MarkD833/RCBUS-68xxx/boards/RC207-68000_BOOTROM_RAM/readme.md

# BOOT ROM & RAM board - 1M ROM + 1M RAM

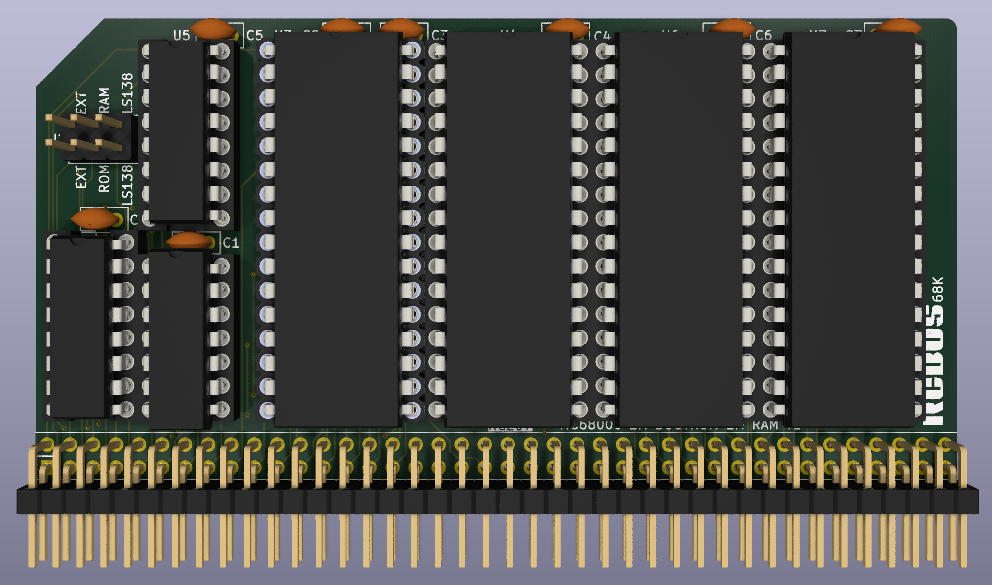
[picture p16: images/RC207-1.png]


The additional 2 chips hidden under one of the ROMs.

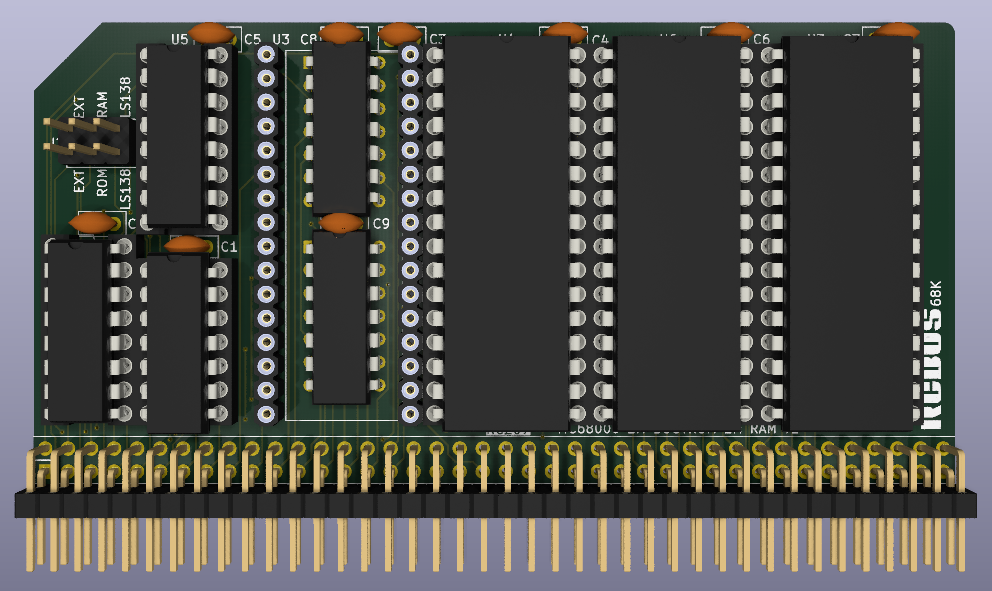
[picture p17: images/RC207-2.png]


# Details
This is a 3D render of my new BOOT ROM & RAM board. It is almost identical to my RC107 board with a couple of exceptions.

I'm experimenting with moving the BOOT ROM so that RAM can be located at address 0x000000. This board places the ROMs at address 0x000000 at reset. The ROMs stay mapped to this address until the first write is detected when the ROMs get mapped to addresses 0x700000..0x7FFFFF and the RAMs become available at addresses 0x000000..0x0FFFFF until the next reset. 

This memory board requires a software write to remap the memory chips.

This is very much a prototype at the moment and I need to see if the manual write works or causes issues.

**NOTE:** Work on this board has been abandoned after the success of RC208 which switches ROM & RAM automatically.
