MarkD833/RCBUS-68xxx/asm_code/ehBASIC_3.54/README.md

# EhBASIC68k for RCBus 68000

Enhanced 68k BASIC Version 3.54 for my RCBus 68000 system.

Assemble using EASy68K.

Original text follows:

---

 EhBASIC68

 Enhanced BASIC is a BASIC interpreter for the 68k family microprocessors. It  
 is constructed to be quick and powerful and easily ported between 68k systems.  
 It requires few resources to run and includes instructions to facilitate easy  
 low level handling of hardware devices. It also retains most of the powerful  
 high level instructions from similar BASICs.  

 EhBASIC is copyright Lee Davison 2002 - 2012 and free for educational or  
 personal use only.  
 For commercial use please contact me at leeedavison@lgooglemail.com for conditions.  

 For more information on EhBASIC68, other versions of EhBASIC and other projects  
 please visit my site at ..  

	 http://mycorner.no-ip.org/index.html  

https://github.com/jefftranter/68000/tree/master/ehbasic

---
## Retro Computing » MOS Technology 6502 » Lee Davison’s website
http://retro.hansotten.nl/6502-sbc/lee-davison-web-site/
