MarkD833/RCBUS-68xxx/asm_code/SC611/25LC256_1.png

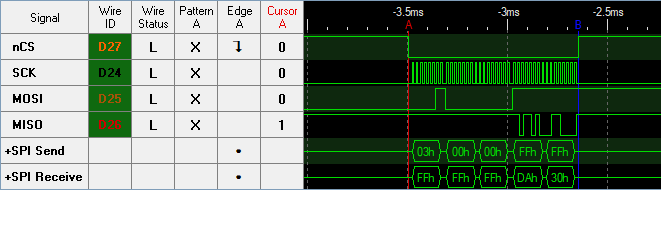
asm_code/SC611/25LC256_1.png
