MarkD833/RCBUS-68xxx/asm_code/SC611/25LC256_2.png

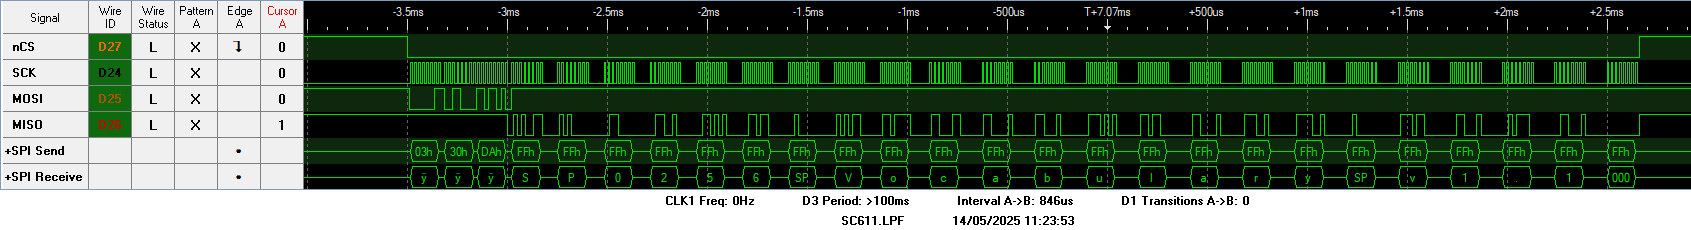
asm_code/SC611/25LC256_2.png
