MarkD833/RCBUS-68xxx/images/Board_Set_2.JPG

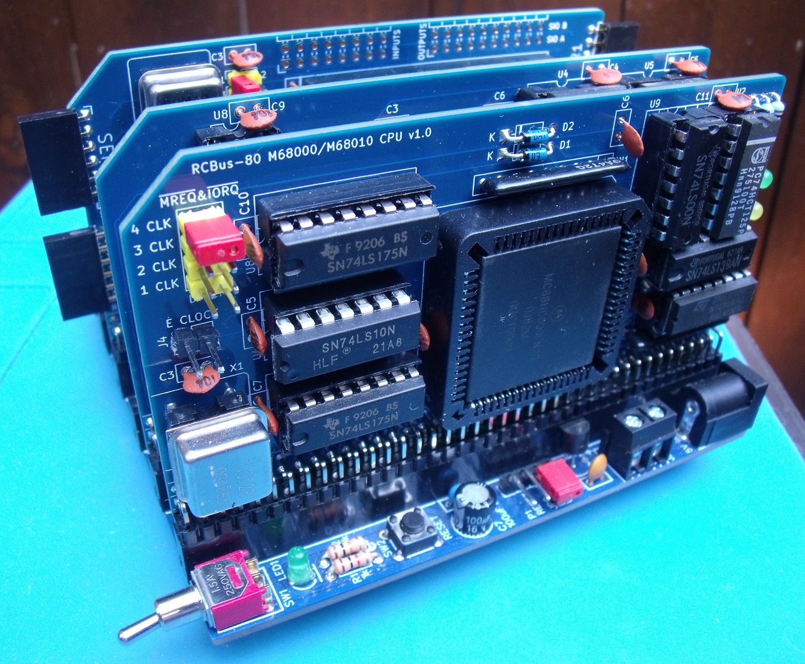
images/Board_Set_2.JPG
