MarkD833/RCBUS-68xxx/images/MC68302_Pins_1.JPG

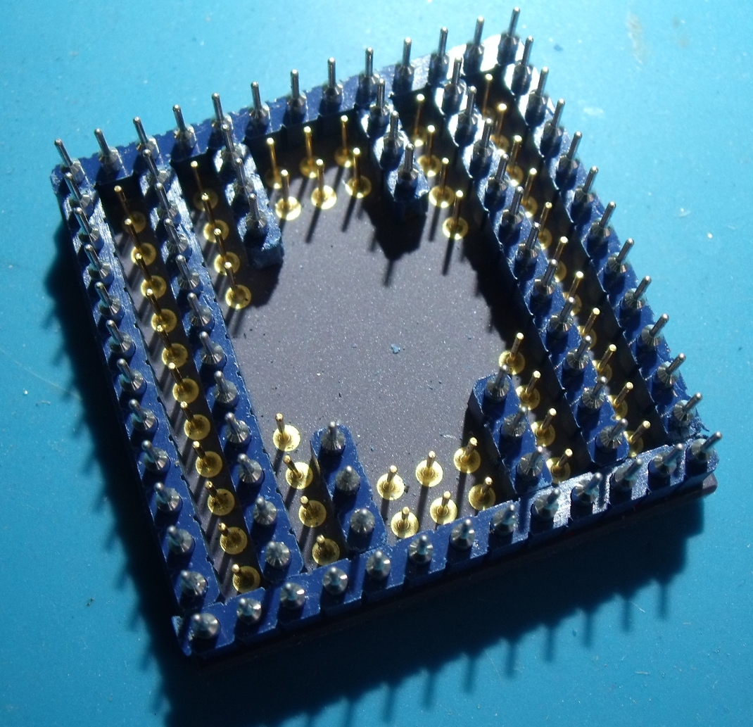
images/MC68302_Pins_1.JPG
