MarkD833/RCBUS-68xxx/images/PIO_Rear.JPG

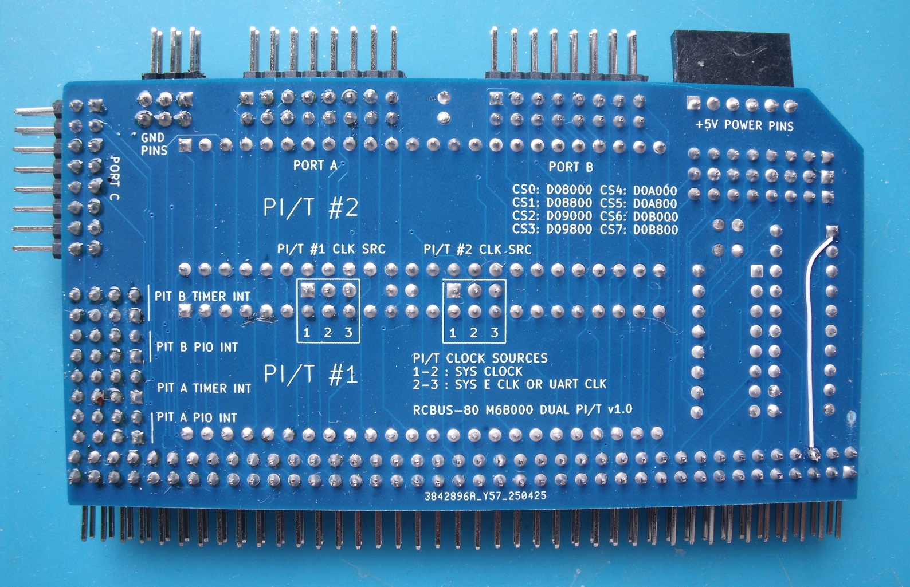
images/PIO_Rear.JPG
