MarkD833/RCBUS-68xxx/images/Processor_Rear.JPG

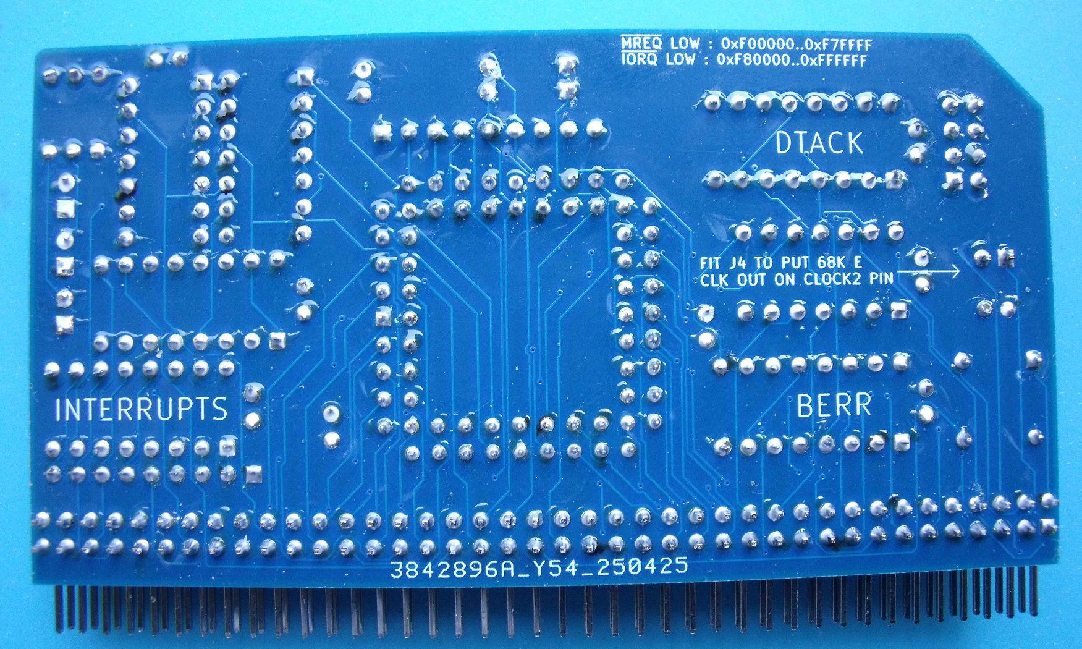
images/Processor_Rear.JPG
