MarkD833/RCBUS-68xxx/images/RC200-Dev_Backplane.png

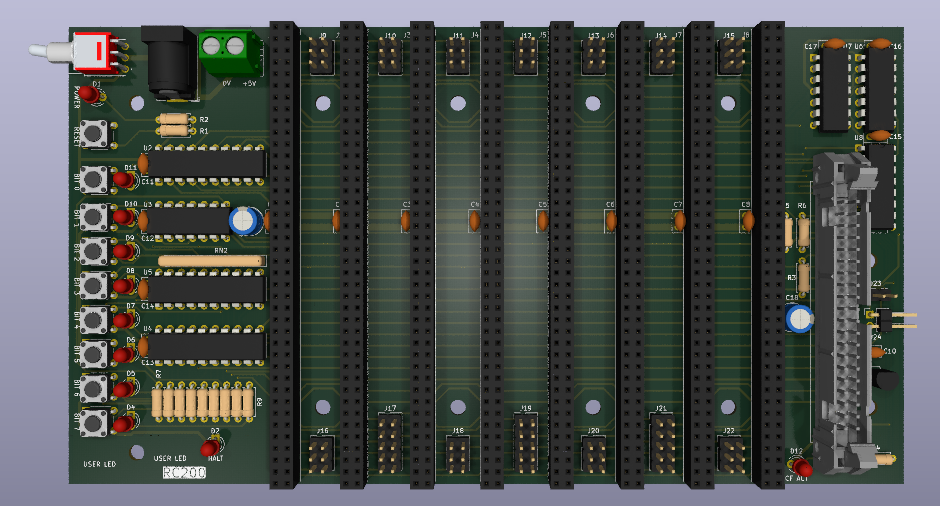
images/RC200-Dev_Backplane.png
