MarkD833/RCBUS-68xxx/images/RC201-68000_CPU_VI_Board_v2.png

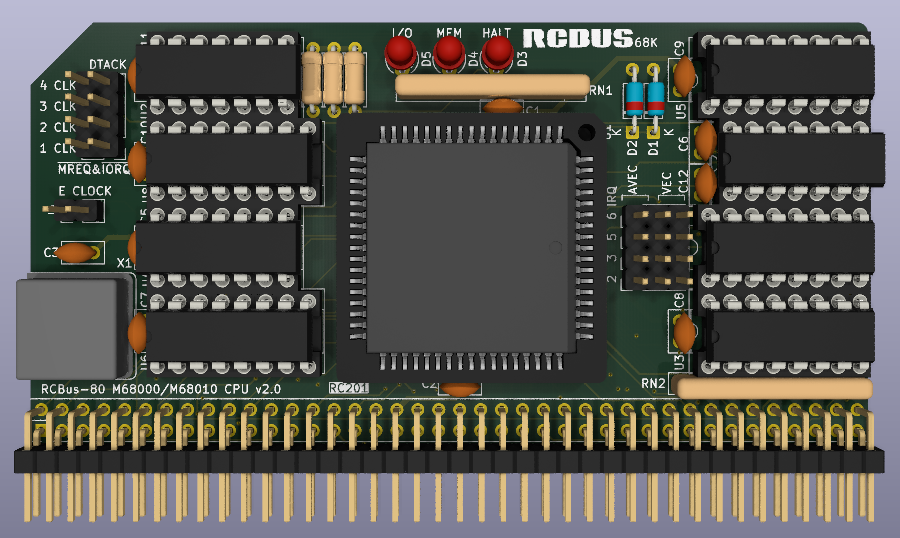
images/RC201-68000_CPU_VI_Board_v2.png
