MarkD833/RCBUS-68xxx/images/RC205-68020_CPU_1.png

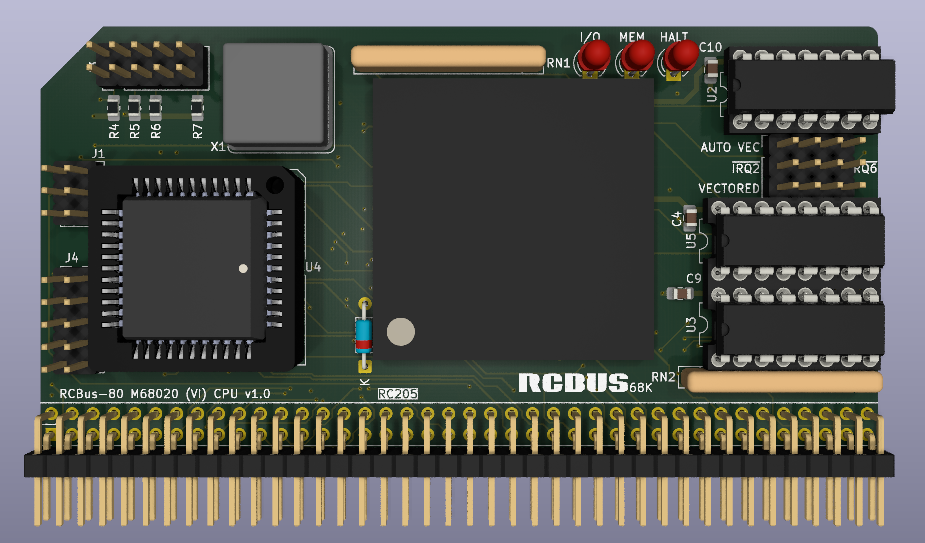
images/RC205-68020_CPU_1.png
