MarkD833/RCBUS-68xxx/images/ROM_RAM_Rear.JPG

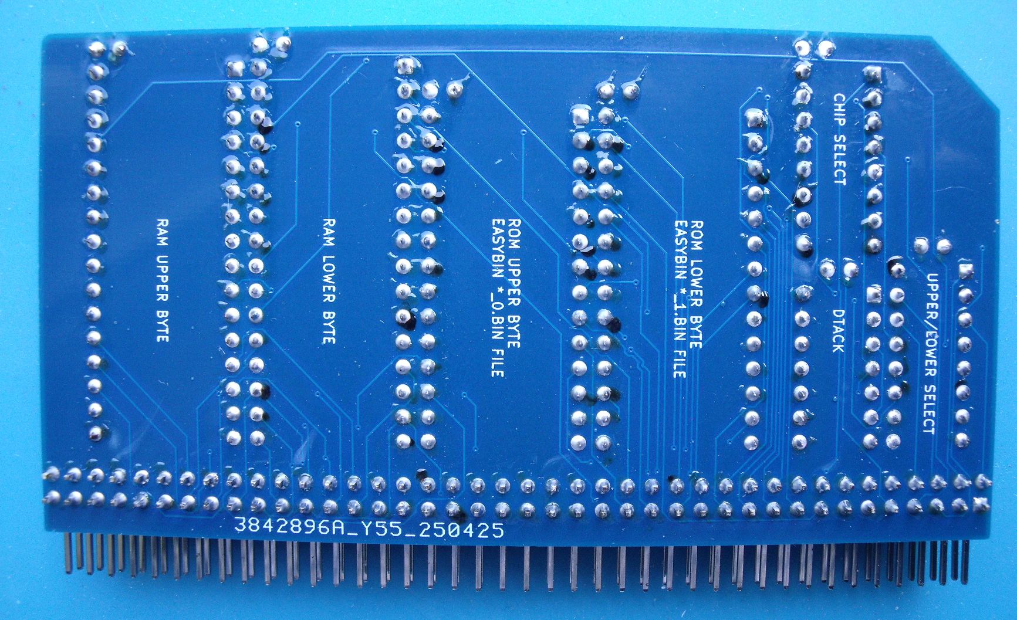
images/ROM_RAM_Rear.JPG
