MarkD833/RCBUS-68xxx/images/S2_68000_PIO_VI_Board.png

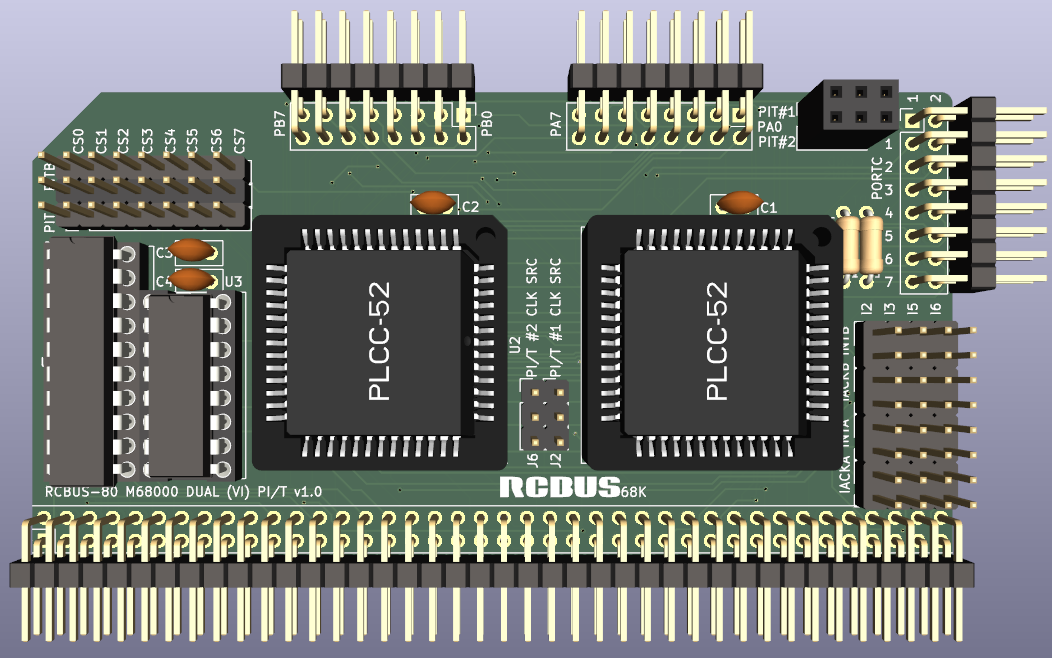
images/S2_68000_PIO_VI_Board.png
