MarkD833/RCBUS-68xxx/images/Serial_Rear.JPG

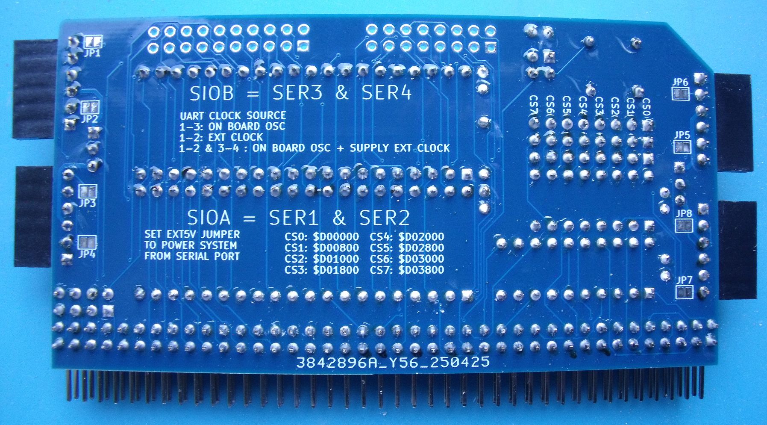
images/Serial_Rear.JPG
