MarkD833/RCBUS-68xxx/boards/RC200-Dev_Backplane/RC200-Dev_Backplane.pdf

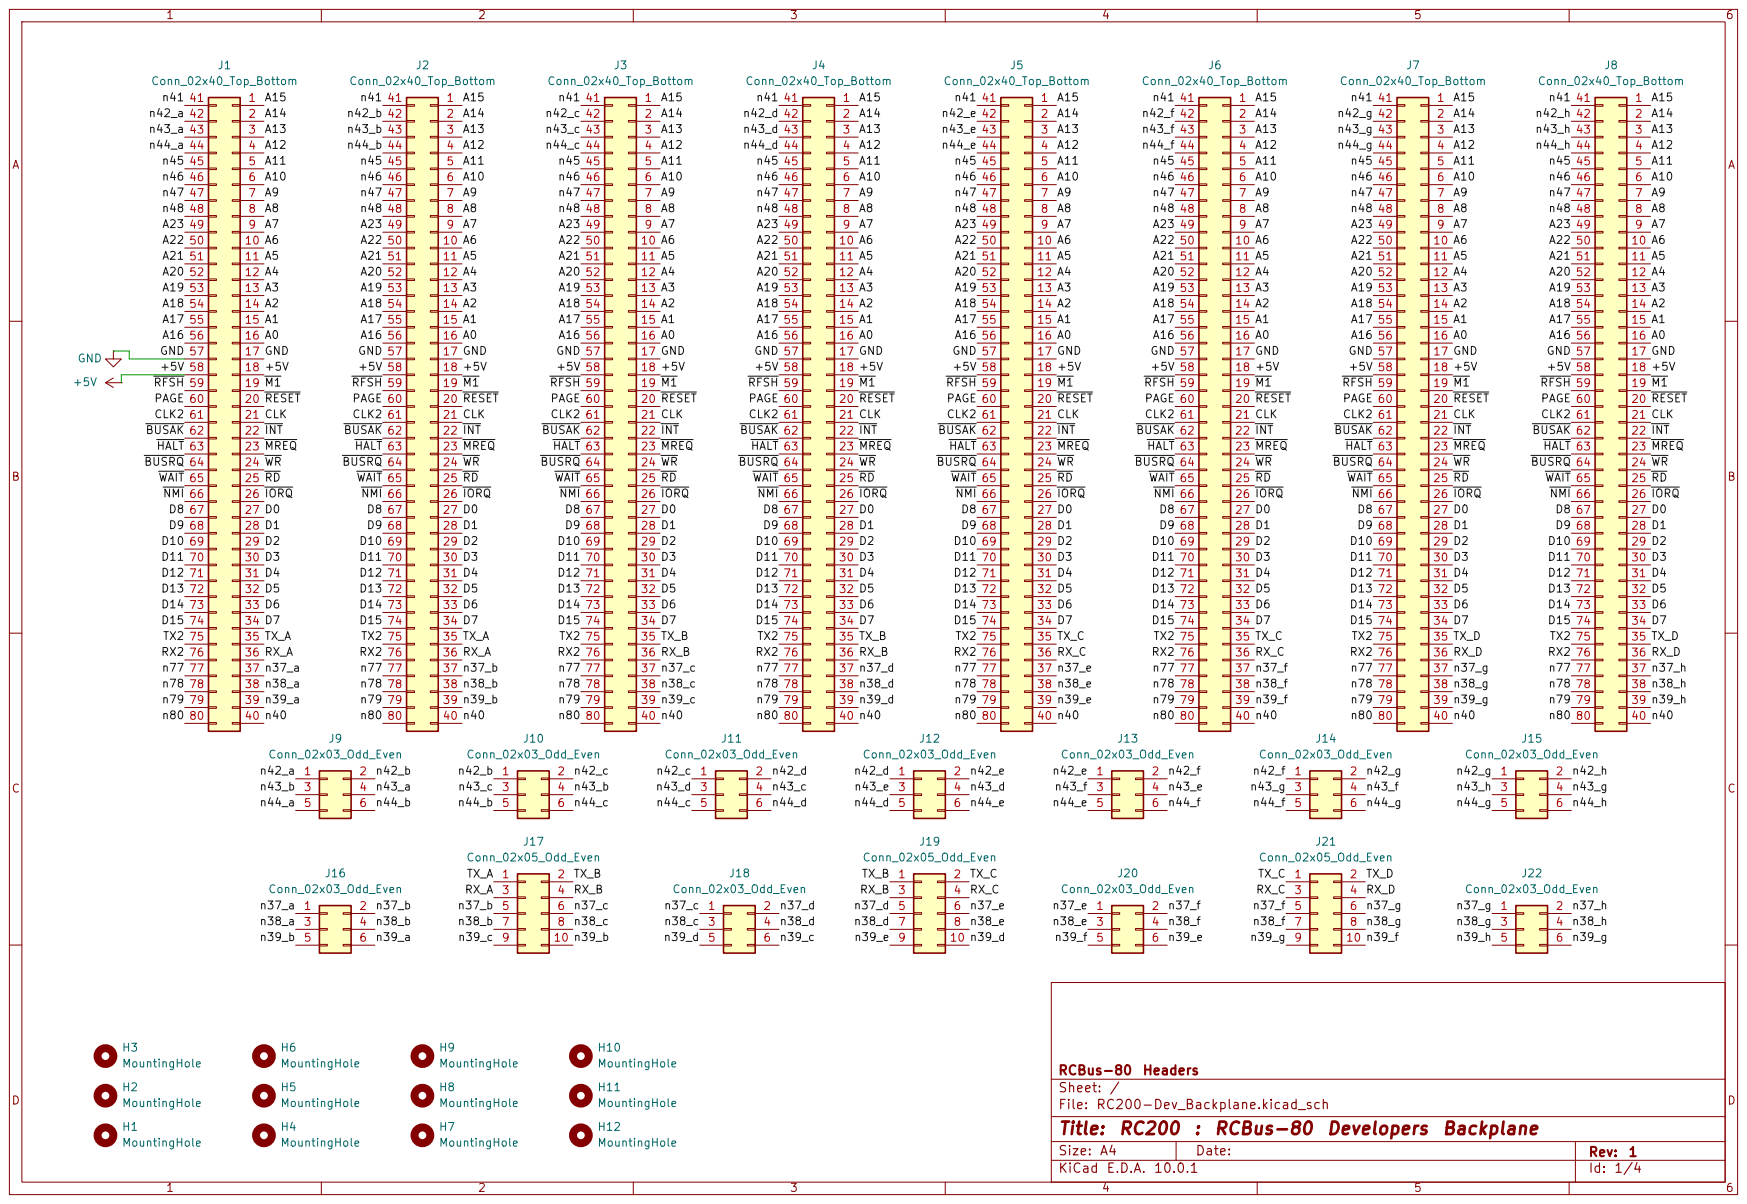
[picture p51: page 1]

RCBus-80 Headers
Sheet: /
File: RC200-Dev_Backplane.kicad_sch
Title: RC200 : RCBus-80 Developers Backplane

Size: A4 | Rev: 1
KiCad E.D.A. 10.0.1 | Id: 1/4

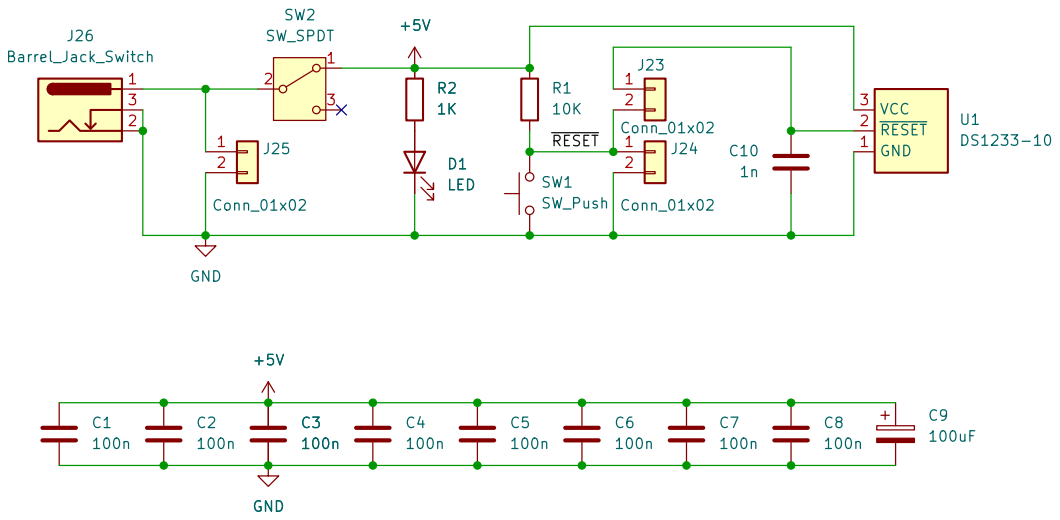
[picture p52: page 2]

Power
Sheet: /
File: power.kicad_sch
Title: RC200 : RCBus-80 Developers Backplane

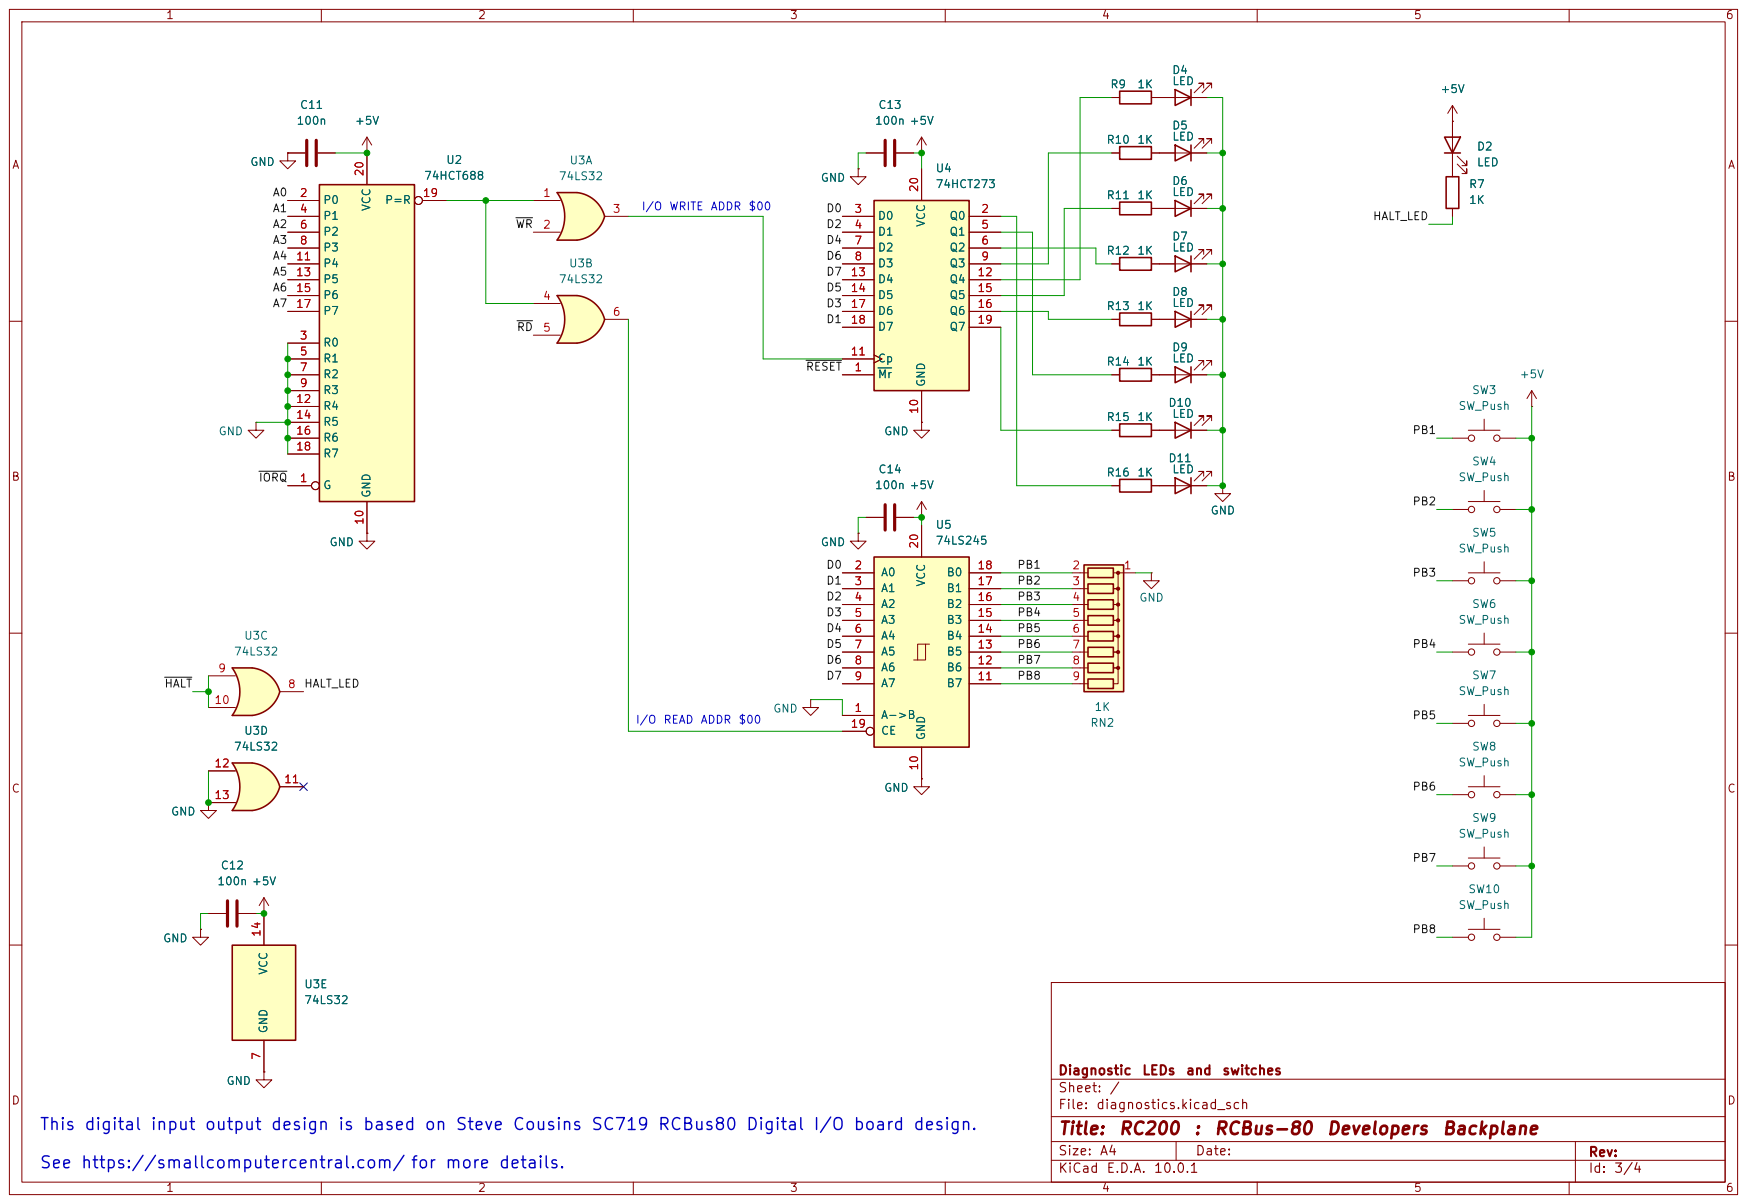
[picture p53: page 3]

Diagnostic LEDs and switches
Sheet: /
File: diagnostics.kicad_sch
Title: RC200 : RCBus-80 Developers Backplane

This digital input output design is based on Steve Cousins SC719 RCBus80 Digital I/O board design.

See https://smallcomputercentral.com/ for more details.

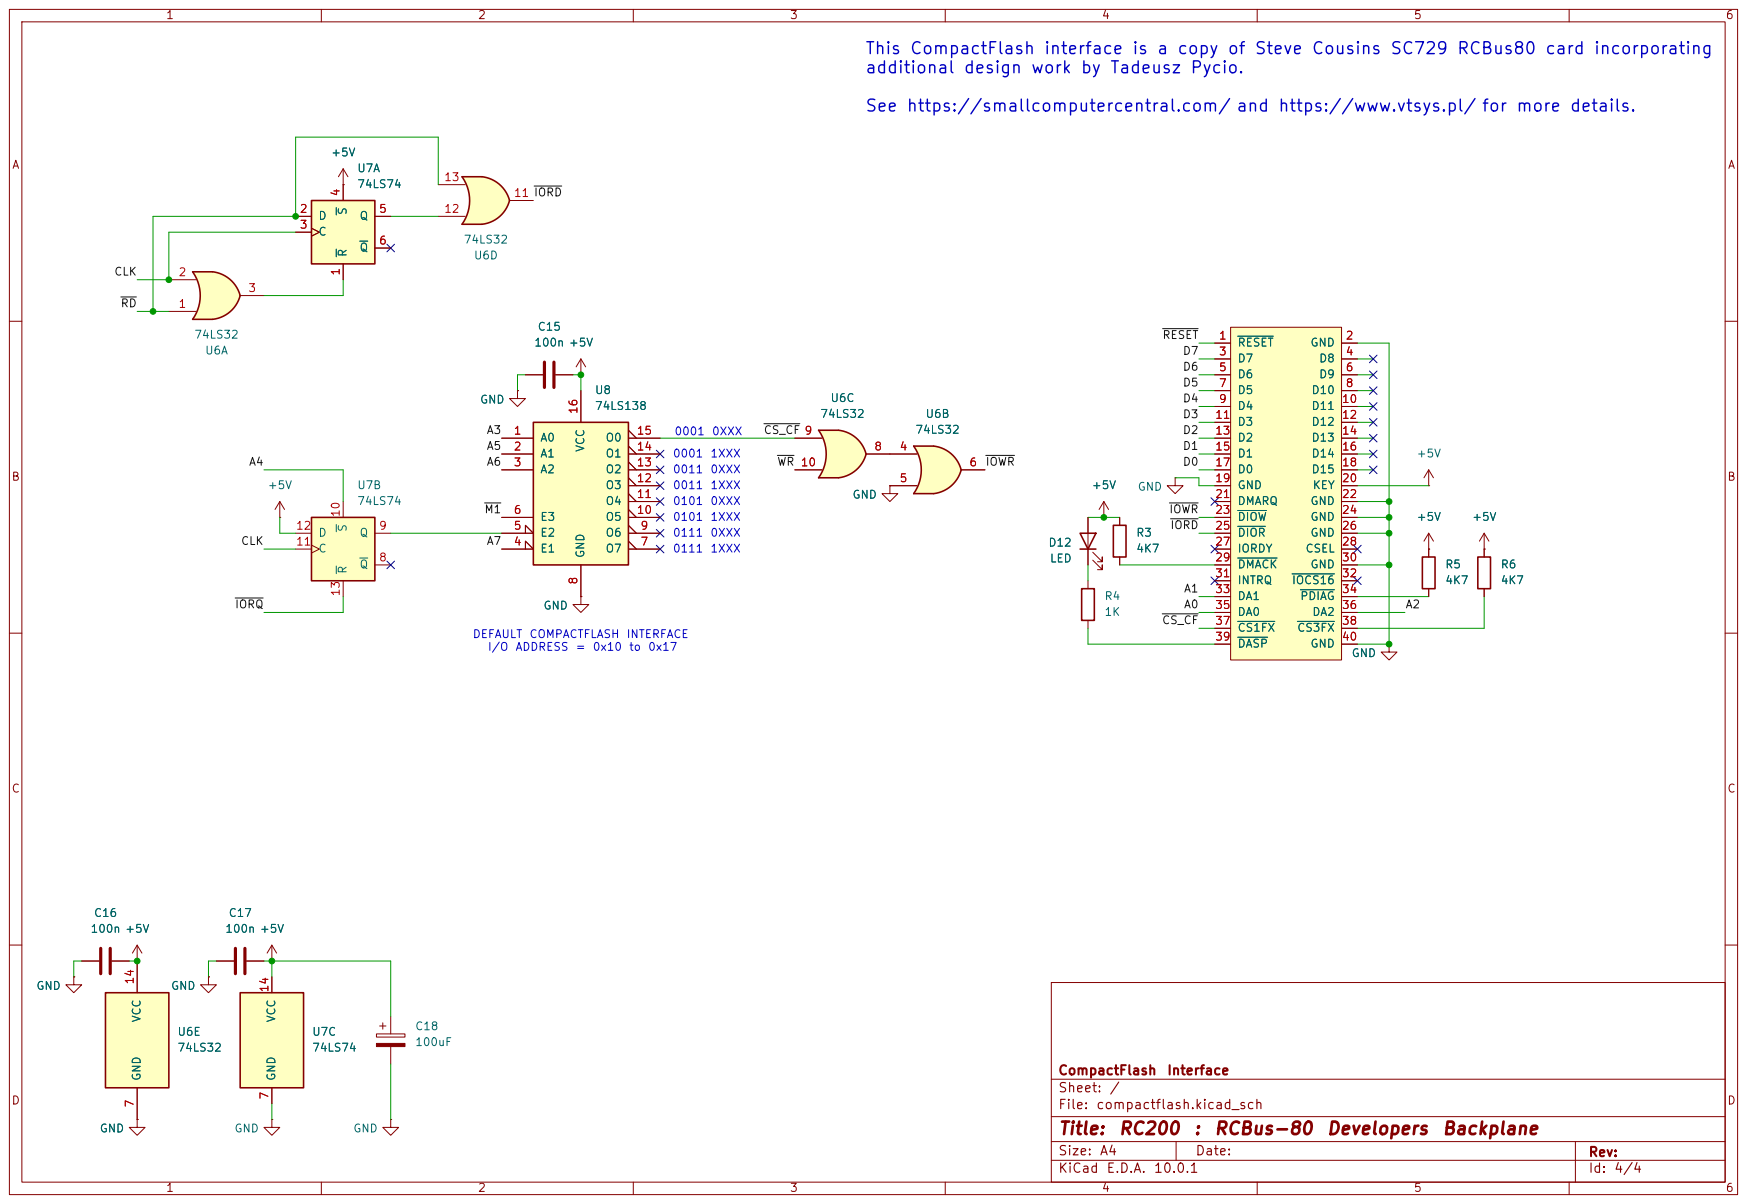
[picture p54: page 4]

additional design work by Tadeusz Pycio.

See https://smallcomputercentral.com/ and https://www.vtsys.pl/ for more details. D12

CompactFlash Interface
Sheet: /
File: compactflash.kicad_sch
Title: RC200 : RCBus-80 Developers Backplane
