MarkD833/RCBUS-68xxx/boards/RC208-68000_BOOTROM_RAM/RC208-68000_BOOTROM_RAM_2.pdf

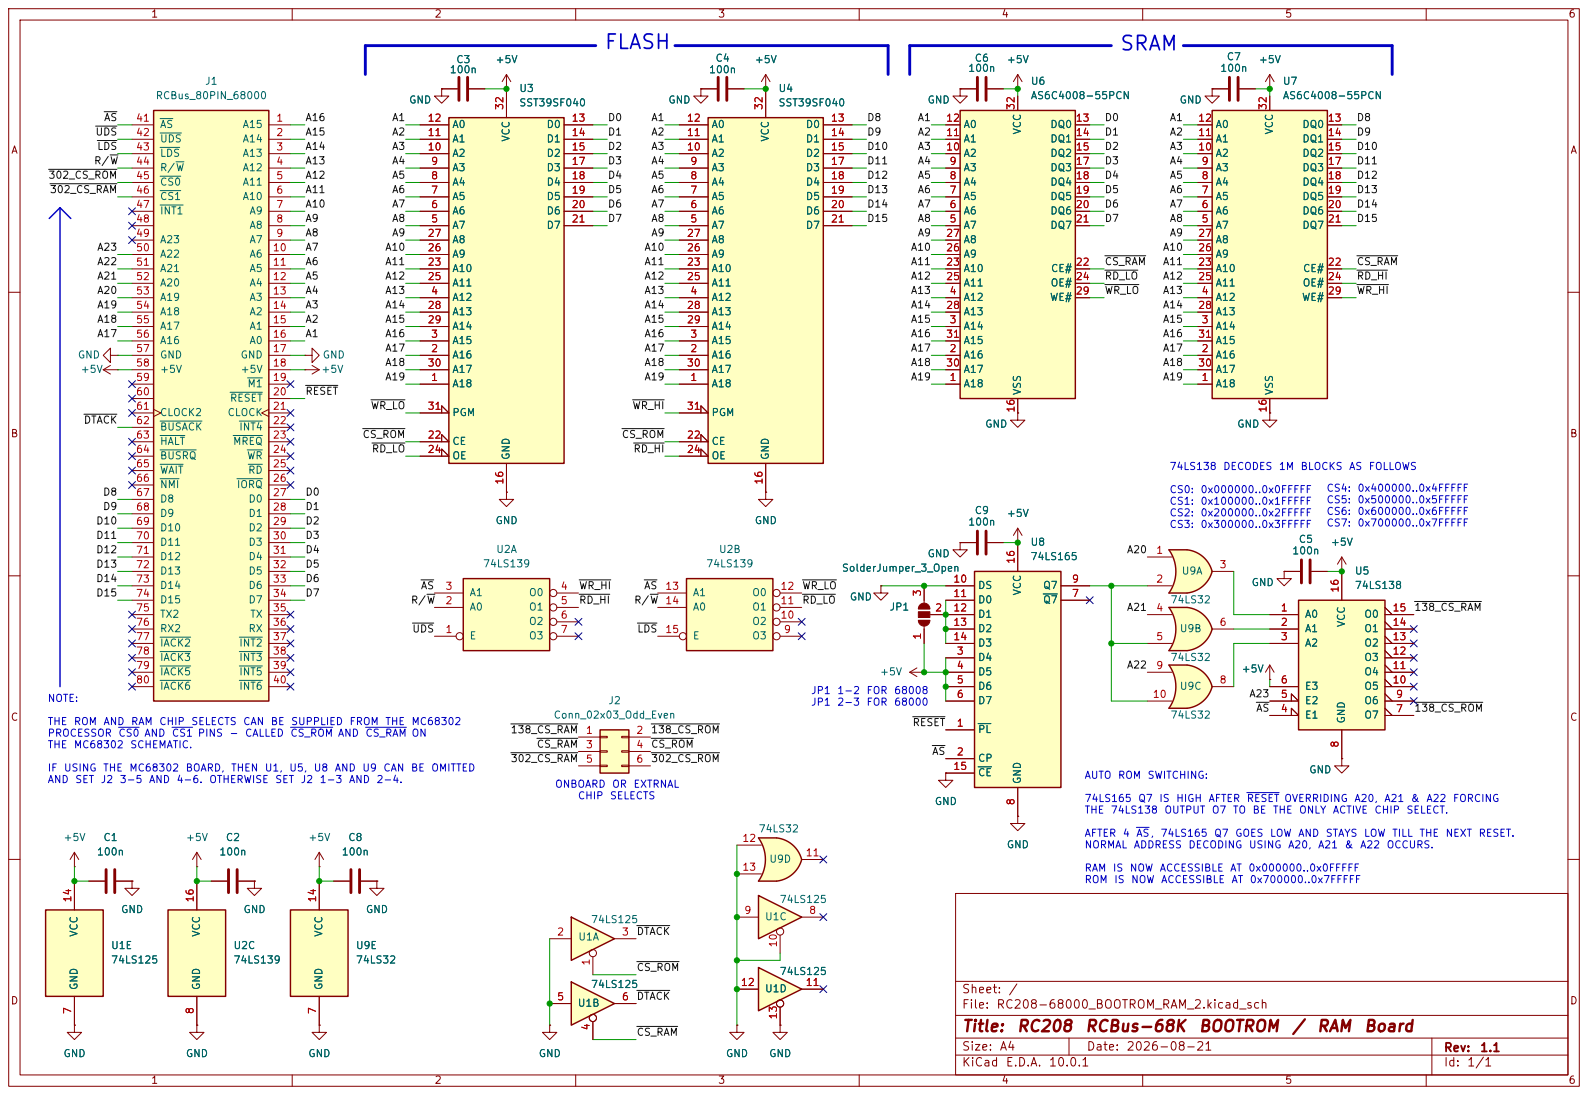
[picture p55: page 1]

74LS138 DECODES 1M BLOCKS AS FOLLOWS CS0: 0x000000..0x0FFFFF CS1: 0x100000..0x1FFFFF CS2: 0x200000..0x2FFFFF CS3: 0x300000..0x3FFFFF FLASH
AS6C4008-55PCN VSS 16 VCC 32
74LS138 VSS 16 VCC 32

CS4: 0x400000..0x4FFFFF CS5: 0x500000..0x5FFFFF CS6: 0x600000..0x6FFFFF CS7: 0x700000..0x7FFFFF NOTE: THE ROM AND RAM CHIP SELECTS CAN BE SUPPLIED FROM THE MC68302 PROCESSOR CS0 AND CS1 PINS - CALLED CS_ROM AND CS_RAM ON

THE 74LS138 OUTPUT O7 TO BE THE ONLY ACTIVE CHIP SELECT. AFTER 4 AS , 74LS165 Q7 GOES LOW AND STAYS LOW TILL THE NEXT RESET. NORMAL ADDRESS DECODING USING A20, A21 & A22 OCCURS. RAM IS NOW ACCESSIBLE AT 0x000000..0x0FFFFF ROM IS NOW ACCESSIBLE AT 0x700000..0x7FFFFF +5V U8

IF USING THE MC68302 BOARD, THEN U1, U5, U8 AND U9 CAN BE OMITTED
100n +5V GNDGND

ONBOARD OR EXTRNAL CHIP SELECTS

Sheet: /
File: RC208-68000_BOOTROM_RAM_2.kicad_sch
Title: RC208 RCBus-68K BOOTROM / RAM Board

Size: A4 | Rev: 1.1
KiCad E.D.A. 10.0.1 | Id: 1/1
