MarkD833/RCBUS-68xxx/boards/RC103_SIO_Board/68000_SIO_BOARD.kicad_pcb

## KiCad design boards/RC103_SIO_Board/68000_SIO_BOARD.kicad_pcb (2025-05-10)

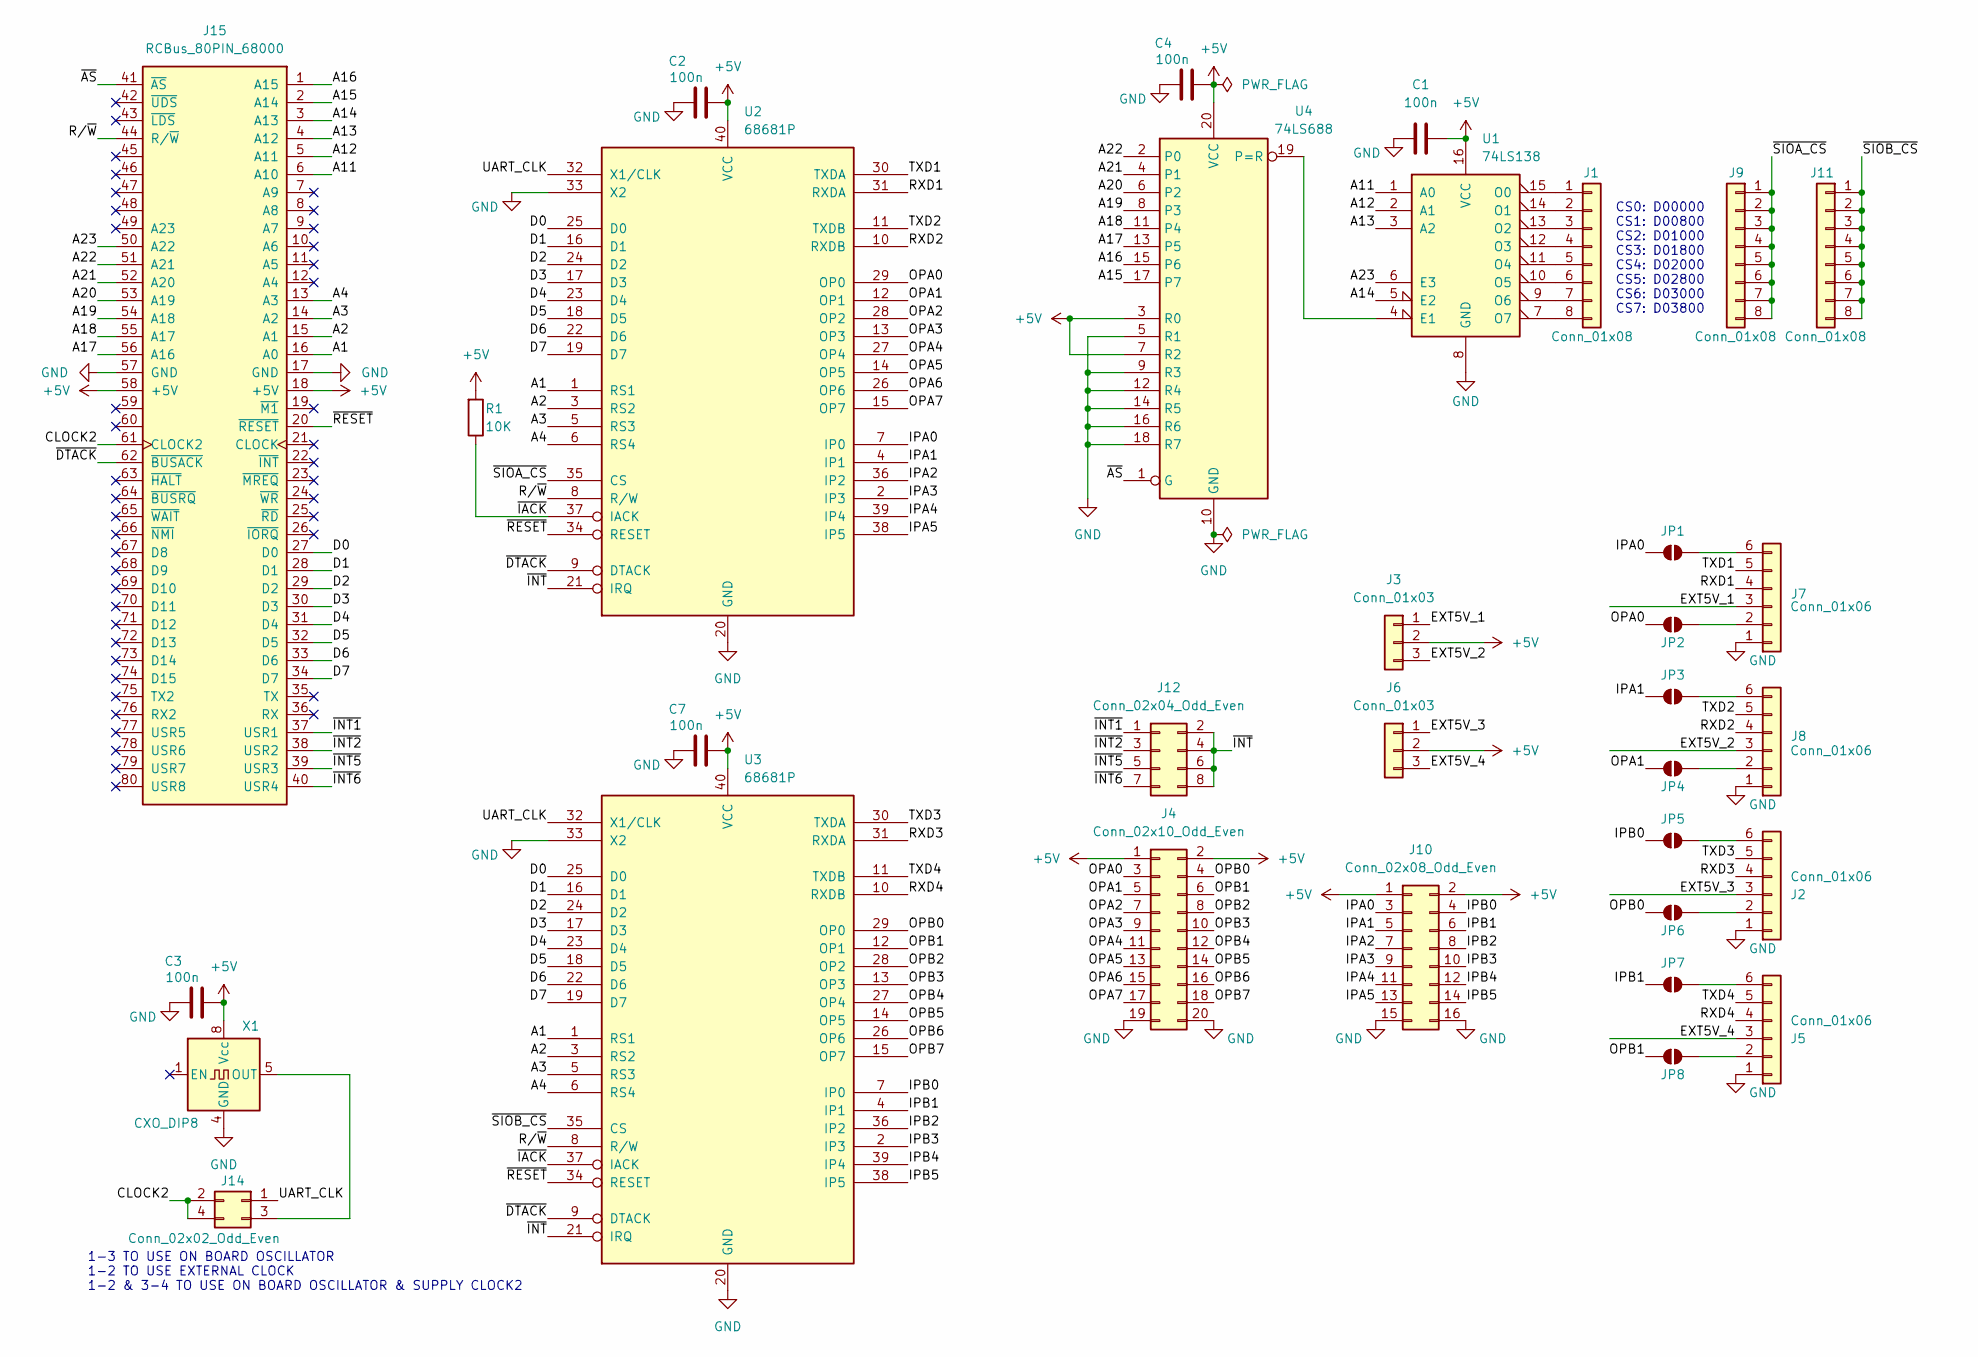
[picture p83: schematic 68000_SIO_BOARD.kicad_sch]

Parts:
C1, C2, C3, C4, C7: 100n; C_Disc_D5.0mm_W2.5mm_P2.50mm
J1, J9, J11: Conn_01x08; PinHeader_1x08_P2.54mm_Vertical
J2, J5, J7, J8: Conn_01x06; PinSocket_1x06_P2.54mm_Horizontal
J3, J6: Conn_01x03; PinHeader_1x03_P2.54mm_Vertical
J4: Conn_02x10_Odd_Even; PinHeader_2x10_P2.54mm_Horizontal
J10: Conn_02x08_Odd_Even; PinHeader_2x08_P2.54mm_Horizontal
J12: Conn_02x04_Odd_Even; PinHeader_2x04_P2.54mm_Vertical
J14: Conn_02x02_Odd_Even; PinHeader_2x02_P2.54mm_Vertical
J15: RCBus_80PIN_68000; RCBus_80p_Medium
JP1, JP2, JP3, JP4, JP5, JP6, JP7, JP8: SolderJumper; SolderJumper-2_P1.3mm_Open_Pad1.0x1.5mm
R1: 10K; R_Axial_DIN0207_L6.3mm_D2.5mm_P7.62mm_Horizontal
U1: 74LS138; DIP-16_W7.62mm_Socket
U2, U3: 68681P; DIP-40_W15.24mm_Socket
U4: 74LS688; DIP-20_W7.62mm_Socket
X1: CXO_DIP8; Oscillator_DIP-8

Connections:
+5V: C1.2, C2.2, C3.2, C4.2, C7.2, J3.2, J4.1, J4.2, J6.2, J10.1, J10.2, J15.18 (+5V), J15.58 (+5V), R1.2, U1.16 (VCC), U2.40 (VCC), U3.40 (VCC), U4.3 (R0), U4.7 (R2), U4.20 (VCC), X1.8 (Vcc)
/A1: J15.16 (A0), U2.1 (RS1), U3.1 (RS1)
/A2: J15.15 (A1), U2.3 (RS2), U3.3 (RS2)
/A3: J15.14 (A2), U2.5 (RS3), U3.5 (RS3)
/A4: J15.13 (A3), U2.6 (RS4), U3.6 (RS4)
/A11: J15.6 (A10), U1.1 (A0)
/A12: J15.5 (A11), U1.2 (A1)
/A13: J15.4 (A12), U1.3 (A2)
/A14: J15.3 (A13), U1.5 (E2)
/A15: J15.2 (A14), U4.17 (P7)
/A16: J15.1 (A15), U4.15 (P6)
/A17: J15.56 (A16), U4.13 (P5)
/A18: J15.55 (A17), U4.11 (P4)
/A19: J15.54 (A18), U4.8 (P3)
/A20: J15.53 (A19), U4.6 (P2)
/A21: J15.52 (A20), U4.4 (P1)
/A22: J15.51 (A21), U4.2 (P0)
/A23: J15.50 (A22), U1.6 (E3)
/CLOCK2: J14.2, J14.4, J15.61 (CLOCK2)
/D0: J15.27 (D0), U2.25 (D0), U3.25 (D0)
/D1: J15.28 (D1), U2.16 (D1), U3.16 (D1)
/D2: J15.29 (D2), U2.24 (D2), U3.24 (D2)
/D3: J15.30 (D3), U2.17 (D3), U3.17 (D3)
/D4: J15.31 (D4), U2.23 (D4), U3.23 (D4)
/D5: J15.32 (D5), U2.18 (D5), U3.18 (D5)
/D6: J15.33 (D6), U2.22 (D6), U3.22 (D6)
/D7: J15.34 (D7), U2.19 (D7), U3.19 (D7)
/EXT5V_1: J3.1, J7.3
/EXT5V_2: J3.3, J8.3
/EXT5V_3: J2.3, J6.1
/EXT5V_4: J5.3, J6.3
/IPA0: J10.3, JP1.1 (A), U2.7 (IP0)
/IPA1: J10.5, JP3.1 (A), U2.4 (IP1)
/IPA2: J10.7, U2.36 (IP2)
/IPA3: J10.9, U2.2 (IP3)
/IPA4: J10.11, U2.39 (IP4)
/IPA5: J10.13, U2.38 (IP5)
/IPB0: J10.4, JP5.1 (A), U3.7 (IP0)
/IPB1: J10.6, JP7.1 (A), U3.4 (IP1)
/IPB2: J10.8, U3.36 (IP2)
/IPB3: J10.10, U3.2 (IP3)
/IPB4: J10.12, U3.39 (IP4)
/IPB5: J10.14, U3.38 (IP5)
/OPA0: J4.3, JP2.1 (A), U2.29 (OP0)
/OPA1: J4.5, JP4.1 (A), U2.12 (OP1)
/OPA2: J4.7, U2.28 (OP2)
/OPA3: J4.9, U2.13 (OP3)
/OPA4: J4.11, U2.27 (OP4)
/OPA5: J4.13, U2.14 (OP5)
/OPA6: J4.15, U2.26 (OP6)
/OPA7: J4.17, U2.15 (OP7)
/OPB0: J4.4, JP6.1 (A), U3.29 (OP0)
/OPB1: J4.6, JP8.1 (A), U3.12 (OP1)
/OPB2: J4.8, U3.28 (OP2)
/OPB3: J4.10, U3.13 (OP3)
/OPB4: J4.12, U3.27 (OP4)
/OPB5: J4.14, U3.14 (OP5)
/OPB6: J4.16, U3.26 (OP6)
/OPB7: J4.18, U3.15 (OP7)
/RXD1: J7.4, U2.31 (RXDA)
/RXD2: J8.4, U2.10 (RXDB)
/RXD3: J2.4, U3.31 (RXDA)
/RXD4: J5.4, U3.10 (RXDB)
/R/~W: J15.44 (R/~W), U2.8 (R/W), U3.8 (R/W)
/TXD1: J7.5, U2.30 (TXDA)
/TXD2: J8.5, U2.11 (TXDB)
/TXD3: J2.5, U3.30 (TXDA)
/TXD4: J5.5, U3.11 (TXDB)
/UART_CLK: J14.1, U2.32 (X1/CLK), U3.32 (X1/CLK)
/~AS: J15.41 (~AS), U4.1 (G)
/~DTACK: J15.62 (~BUSACK), U2.9 (DTACK), U3.9 (DTACK)
/~IACK: R1.1, U2.37 (IACK), U3.37 (IACK)
/~INT1: J12.1, J15.37 (USR1)
/~INT2: J12.3, J15.38 (USR2)
/~INT5: J12.5, J15.39 (USR3)
/~INT6: J12.7, J15.40 (USR4)
/~INT: J12.2, J12.4, J12.6, J12.8, U2.21 (IRQ), U3.21 (IRQ)
/~RESET: J15.20 (~RESET), U2.34 (RESET), U3.34 (RESET)
/~SIOA_CS: J9.1, J9.2, J9.3, J9.4, J9.5, J9.6, J9.7, J9.8, U2.35 (CS)
/~SIOB_CS: J11.1, J11.2, J11.3, J11.4, J11.5, J11.6, J11.7, J11.8, U3.35 (CS)
GND: C1.1, C2.1, C3.1, C4.1, C7.1, J2.1, J4.19, J4.20, J5.1, J7.1, J8.1, J10.15, J10.16, J15.17 (GND), J15.57 (GND), U1.8 (GND), U2.20 (GND), U2.33 (X2), U3.20 (GND), U3.33 (X2), U4.5 (R1), U4.9 (R3), U4.10 (GND), U4.12 (R4), U4.14 (R5), U4.16 (R6), U4.18 (R7), X1.4 (GND)
unnamed: J1.1, U1.15 (O0)
unnamed: J1.2, U1.14 (O1)
unnamed: J1.3, U1.13 (O2)
unnamed: J1.4, U1.12 (O3)
unnamed: J1.5, U1.11 (O4)
unnamed: J1.6, U1.10 (O5)
unnamed: J1.7, U1.9 (O6)
unnamed: J1.8, U1.7 (O7)
unnamed: J2.2, JP6.2 (B)
unnamed: J2.6, JP5.2 (B)
unnamed: J5.2, JP8.2 (B)
unnamed: J5.6, JP7.2 (B)
unnamed: J7.2, JP2.2 (B)
unnamed: J7.6, JP1.2 (B)
unnamed: J8.2, JP4.2 (B)
unnamed: J8.6, JP3.2 (B)
unnamed: J14.3, X1.5 (OUT)
unnamed: U1.4 (E1), U4.19 (P=R)

Notes on the sheet:
CS0: D00000 CS1: D00800 CS2: D01000 CS3: D01800 CS4: D02000 CS5: D02800 CS6: D03000 CS7: D03800
1-3 TO USE ON BOARD OSCILLATOR 1-2 TO USE EXTERNAL CLOCK 1-2 & 3-4 TO USE ON BOARD OSCILLATOR & SUPPLY CLOCK2

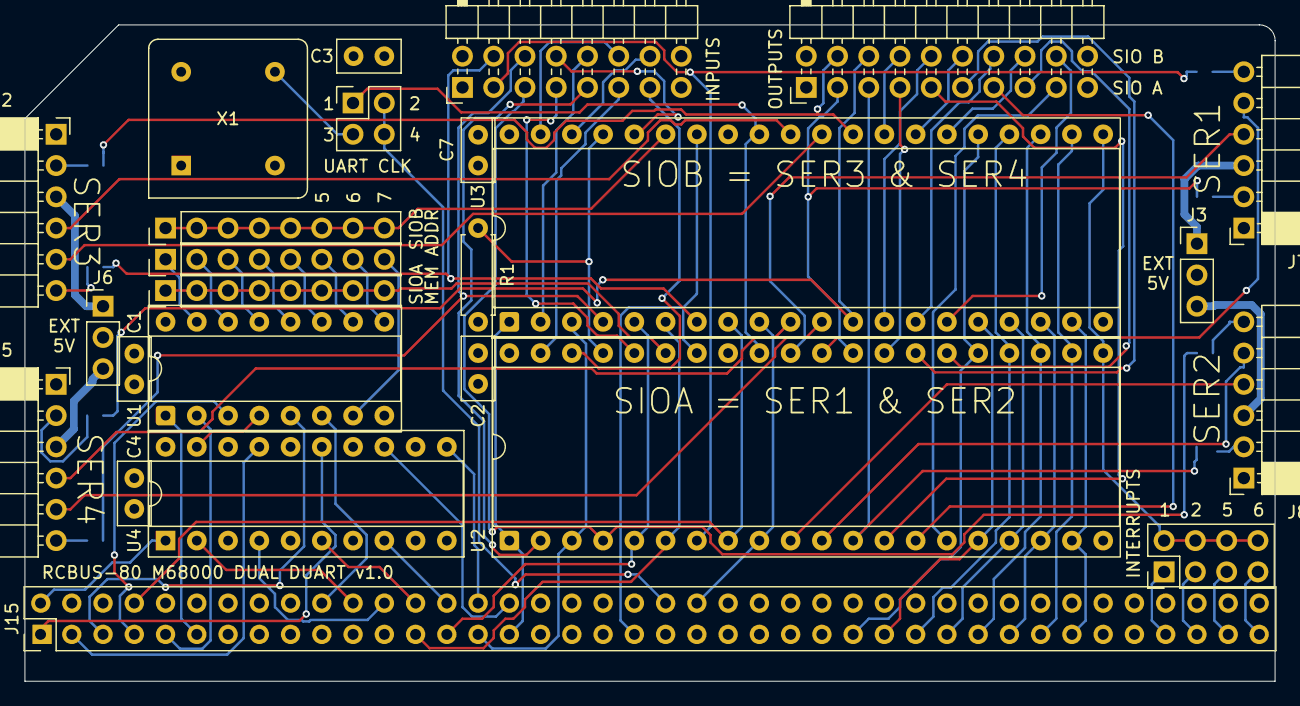
[picture p84: board 68000_SIO_BOARD.kicad_pcb from above]

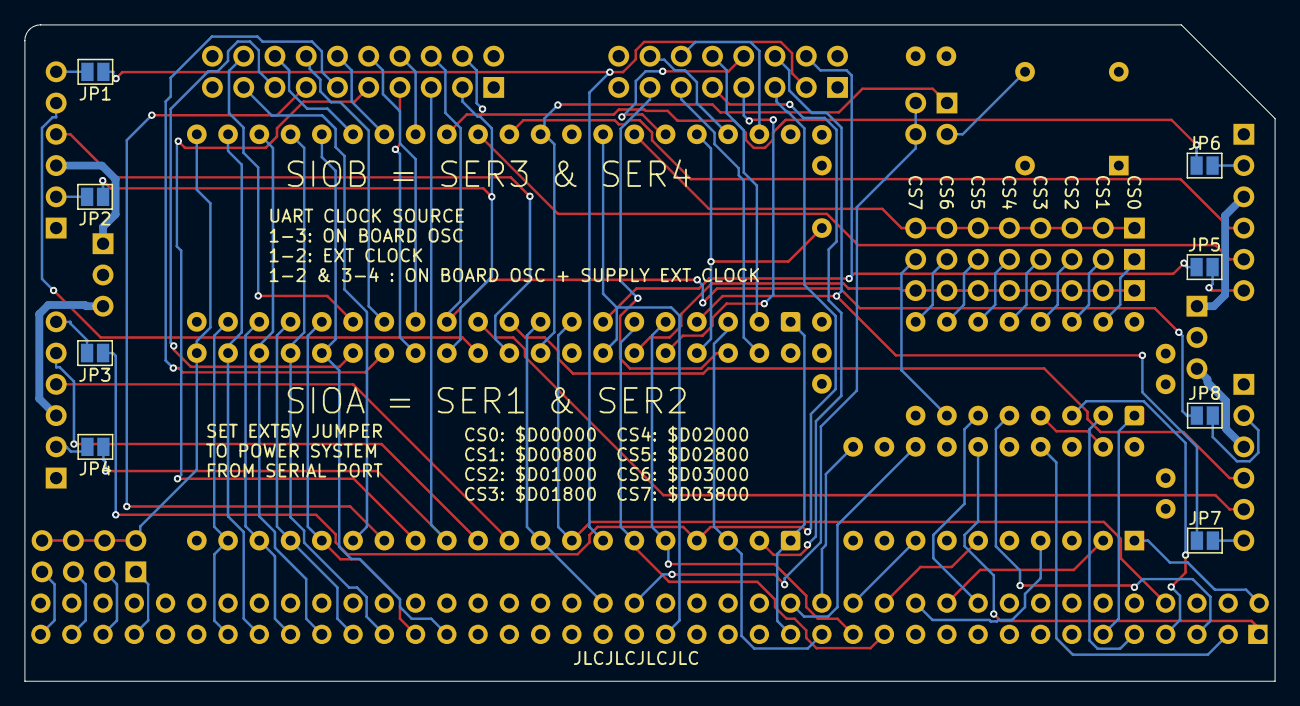
[picture p85: board 68000_SIO_BOARD.kicad_pcb from below]

Board: 4 copper layers, 101.6 x 53.3 mm, 33 parts (8 on the bottom side), 99 nets.
