MarkD833/RCBUS-68xxx/c_code/TMS9918A_Nyan/nyan.c

/* D:\Micros\M68K\RCBUS_68000\TMS9918A\nyan\nyan.bin (22/10/2022 17:09:30)
   StartOffset(h): 00000000, EndOffset(h): 000047FF, Length(h): 00004800 */

#include <stdint.h>

unsigned char rawData[18432] = {
	0x44, 0x44, 0x44, 0x44, 0x44, 0x44, 0x44, 0x44, 0x44, 0x44, 0x44, 0x44,
	0x44, 0x44, 0x44, 0x44, 0x44, 0x44, 0x44, 0x44, 0x44, 0x44, 0x44, 0x44,
	0x44, 0x44, 0x44, 0x44, 0x44, 0x44, 0x44, 0x44, 0x44, 0x44, 0x44, 0x44,
	0x44, 0x44, 0x44, 0x44, 0x44, 0x44, 0x44, 0x44, 0x44, 0x44, 0x44, 0x44,
	0x44, 0x44, 0x44, 0x44, 0x44, 0x44, 0x44, 0x44, 0x44, 0x44, 0x44, 0x44,
	0x44, 0x44, 0x44, 0x44, 0x44, 0x44, 0x44, 0x44, 0x44, 0x44, 0x44, 0x44,
	0x44, 0x44, 0x44, 0x44, 0x44, 0x44, 0x44, 0x44, 0x44, 0x44, 0x44, 0x44,
	0x44, 0x44, 0x44, 0x44, 0x44, 0x44, 0x44, 0x44, 0x44, 0x44, 0x44, 0x44,
	0x44, 0x44, 0x44, 0x44, 0x44, 0x44, 0x44, 0x44, 0x44, 0x44, 0x44, 0x44,
	0x44, 0x44, 0x44, 0x44, 0x44, 0x44, 0x44, 0x44, 0x44, 0x44, 0x44, 0x44,
	0x44, 0x44, 0x44, 0x44, 0x44, 0x44, 0x44, 0x44, 0x44, 0x44, 0x44, 0x44,
	0x44, 0x44, 0x44, 0x44, 0x44, 0x44, 0x44, 0x44, 0x44, 0x44, 0x44, 0x44,
	0x44, 0x44, 0x44, 0x44, 0x44, 0x44, 0x44, 0x44, 0x44, 0x44, 0x44, 0x44,
	0x44, 0x44, 0x44, 0x44, 0x44, 0x44, 0x44, 0x44, 0x44, 0x44, 0x44, 0x44,
	0x44, 0x44, 0x44, 0x44, 0x44, 0x44, 0x44, 0x44, 0x44, 0x44, 0x44, 0x44,
	0x44, 0x44, 0x44, 0x44, 0x44, 0x44, 0x44, 0x44, 0x44, 0x44, 0x44, 0x44,
	0x44, 0x44, 0x44, 0x44, 0x44, 0x44, 0x44, 0x44, 0x44, 0x44, 0x44, 0x44,
	0x44, 0x44, 0x44, 0x44, 0x44, 0x44, 0x44, 0x44, 0x44, 0x44, 0x44, 0x44,
	0x44, 0x44, 0x44, 0x44, 0x44, 0x44, 0x44, 0x44, 0x44, 0x44, 0x44, 0x44,
	0x44, 0x44, 0x44, 0x44, 0x44, 0x44, 0x44, 0x44, 0x44, 0x44, 0x44, 0x44,
	0x44, 0x44, 0x44, 0x44, 0x44, 0x44, 0x44, 0x44, 0x44, 0x44, 0x44, 0x44,
	0x44, 0x44, 0x44, 0x44, 0x44, 0x44, 0xF4, 0x4F, 0xF4, 0x44, 0x44, 0x44,
	0x44, 0x44, 0x44, 0x44, 0x44, 0x44, 0x44, 0x66, 0x44, 0x44, 0x44, 0x44,
	0x44, 0x44, 0x44, 0x66, 0x44, 0x44, 0x44, 0x44, 0x44, 0x44, 0x44, 0x66,
	0x44, 0x44, 0x44, 0x44, 0x44, 0x44, 0x44, 0x66, 0x44, 0x44, 0x44, 0x44,
	0x44, 0x44, 0x44, 0x44, 0x44, 0x44, 0x44, 0x44, 0x44, 0x44, 0x44, 0x44,
	0x44, 0x44, 0x44, 0x44, 0x44, 0x44, 0x44, 0x44, 0x44, 0x44, 0x44, 0x44,
	0x44, 0x44, 0x44, 0x44, 0x44, 0x44, 0x44, 0x44, 0x44, 0x44, 0x44, 0x66,
	0x44, 0x44, 0x44, 0x44, 0x44, 0x44, 0x44, 0x66, 0x44, 0x44, 0x44, 0x44,
	0x44, 0x44, 0x44, 0x66, 0x44, 0x44, 0x44, 0x44, 0x44, 0x44, 0x44, 0x61,
	0x44, 0x44, 0x44, 0x44, 0x44, 0x44, 0x11, 0xBB, 0x44, 0x44, 0x44, 0x44,
	0x44, 0x44, 0x11, 0xBB, 0x44, 0x44, 0x44, 0x44, 0x44, 0x44, 0x11, 0xBB,
	0x44, 0x44, 0x44, 0x44, 0x44, 0x44, 0x11, 0xBB, 0x44, 0x44, 0x44, 0x44,
	0x44, 0x44, 0x11, 0xBB, 0x44, 0x44, 0x44, 0x44, 0x44, 0x44, 0x11, 0xBB,
	0x44, 0x44, 0x44, 0x44, 0x44, 0x44, 0x11, 0xBB, 0x44, 0x44, 0x44, 0x44,
	0x44, 0x44, 0x11, 0xBB, 0x44, 0x44, 0x44, 0x44, 0x44, 0x44, 0x14, 0xB1,
	0x44, 0x44, 0x44, 0x44, 0x44, 0x44, 0x44, 0x44, 0x44, 0x44, 0x44, 0x44,
	0x44, 0x44, 0x44, 0x44, 0x44, 0x44, 0x44, 0x44, 0x44, 0x44, 0x44, 0x44,
	0x44, 0x44, 0x44, 0x44, 0x44, 0x44, 0x44, 0x44, 0x44, 0x44, 0x44, 0x44,
	0x44, 0x44, 0x44, 0x44, 0x44, 0x44, 0x44, 0x44, 0x44, 0x44, 0x44, 0x44,
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
};

uint16_t rawSize = sizeof(rawData);
