MarkD833/RCBUS-68xxx/c_code/TMS9918A_ASCII_Chars/tmsfont.h

/******************************************************************************
* RCBus MC68000
*******************************************************************************
* #######  #     #   #####    #####    #####     #     #####      #    
*     #     ##   ##  #     #  #     #  #     #   ##    #     #    # #   
*     #     # # # #  #        #     #  #     #  # #    #     #   #   #  
*     #     #  #  #   #####    ######   ######    #     #####   #     # 
*     #     #     #        #        #        #    #    #     #  ####### 
*     #     #     #  #     #  #     #  #     #    #    #     #  #     # 
*     #     #     #   #####    #####    #####   #####   #####   #     #
*******************************************************************************
* 6x8 bitmap font by Oleg Kosenkov
* Source: https://github.com/idispatch/raster-fonts/blob/master/font-6x8.c
******************************************************************************/

const uint8_t font[] = {
	// code=0, hex=0x00, ascii="^@"
	0b00000000,
	0b00000000,
	0b00000000,
	0b00000000,
	0b00000000,
	0b00000000,
	0b00000000,
	0b00000000,

	// code=1, hex=0x01, ascii="^A"
	0b00111000,
	0b01000100,
	0b01101100,
	0b01000100,
	0b01010100,
	0b01000100,
	0b00111000,
	0b00000000,

	// code=2, hex=0x02, ascii="^B"
	0b00111000,
	0b01111100,
	0b01010100,
	0b01111100,
	0b01000100,
	0b01111100,
	0b00111000,
	0b00000000,

	// code=3, hex=0x03, ascii="^C"
	0b00000000,
	0b00101000,
	0b01111100,
	0b01111100,
	0b01111100,
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
	0b00000000,

	// code=254, hex=0xFE, ascii="!~"
	0b00000000,
	0b00000000,
	0b01111000,
	0b01111000,
	0b01111000,
	0b01111000,
	0b00000000,
	0b00000000,

	// code=255, hex=0xFF, ascii="!^"
	0b00000000,
	0b00000000,
	0b00000000,
	0b00000000,
	0b00000000,
	0b00000000,
	0b00000000,
	0b00000000
};
